Amaziran/balanced_car1/BSP/OLED/oledfont.h

#ifndef __OLEDFONT_H__
#define __OLEDFONT_H__
 
#include "stm32f1xx_hal.h"


const unsigned char  OLED_init_cmd[25]=			//SH1106
{
  
  /*0xae,0X00,0X10,0x40,0X81,0XCF,0xff,0xa1,0xa4,
  0xA6,0xc8,0xa8,0x3F,0xd5,0x80,0xd3,0x00,0XDA,0X12,
  0x8d,0x14,0xdb,0x40,0X20,0X02,0xd9,0xf1,0xAF*/
       0xAE,//关闭显示
	
       0xD5,//设置时钟分频因子,震荡频率
       0x80,  //[3:0],分频因子;[7:4],震荡频率

       0xA8,//设置驱动路数
       0X3F,//默认(1/64)
	
       0xD3,//设置显示偏移
       0X00,//默认为0
	
       0x40,//设置显示开始行 [5:0],行数.
	
       0x8D,//电荷泵设置
       0x14,//bit2，开启/关闭
       0x20,//设置内存地址模式
       0x02,//[1:0],00，列地址模式;01，行地址模式;10,页地址模式;默认10;
       0xA1,//段重定义设置,bit0:0,0->0;1,0->127;  A1
	
       0xC8,//设置COM扫描方向;bit3:0,普通模式;1,重定义模式 COM[N-1]->COM0;N:驱动路数 (C0 翻转显示) C8
	   
       0xDA,//设置COM硬件引脚配置
       0x12,//[5:4]配置  
	   
       0x81,//对比度设置
       0x66,//1~255;默认0X7F (亮度设置,越大越亮)
	   
       0xD9,//设置预充电周期
       0xf1,//[3:0],PHASE 1;[7:4],PHASE 2;
	   
       0xDB,//设置VCOMH 电压倍率
       0x30,//[6:4] 000,0.65*vcc;001,0.77*vcc;011,0.83*vcc;
	   
       0xA4,//全局显示开启;bit0:1,开启;0,关闭;(白屏/黑屏)
	   
       0xA6,//设置显示方式;bit0:1,反相显示;0,正常显示 
       
       0xAF,//开启显示     
};


//8*6 ASCII字符集点阵
const unsigned char F6x8[][6] =		
{
	0x00, 0x00, 0x00, 0x00, 0x00, 0x00,// sp
	0x00, 0x00, 0x00, 0x2f, 0x00, 0x00,// !
	0x00, 0x00, 0x07, 0x00, 0x07, 0x00,// "
	0x00, 0x14, 0x7f, 0x14, 0x7f, 0x14,// #
	0x00, 0x24, 0x2a, 0x7f, 0x2a, 0x12,// $
	0x00, 0x62, 0x64, 0x08, 0x13, 0x23,// %
	0x00, 0x36, 0x49, 0x55, 0x22, 0x50,// &
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
	/* (16 X 16 , 宋体 )*/

	{0x00,0x00,0x00,0x00,0x00,0x00,0x00,0x00,0x00,0x00,0x00,0x00,0x00,0x00,0x00,0x00},
	{0x00,0x00,0x36,0x36,0x00,0x00,0x00,0x00,0x00,0x00,0x00,0x00,0x00,0x00,0x00,0x00},/*"：",6*/
/* (16 X 16 , 宋体 )*/
};

#endif
